MadhuraChoudhary/GuardianSense-AI_Health_Monitor_system/COMPONENT INTERACTION DIAGRAM.png

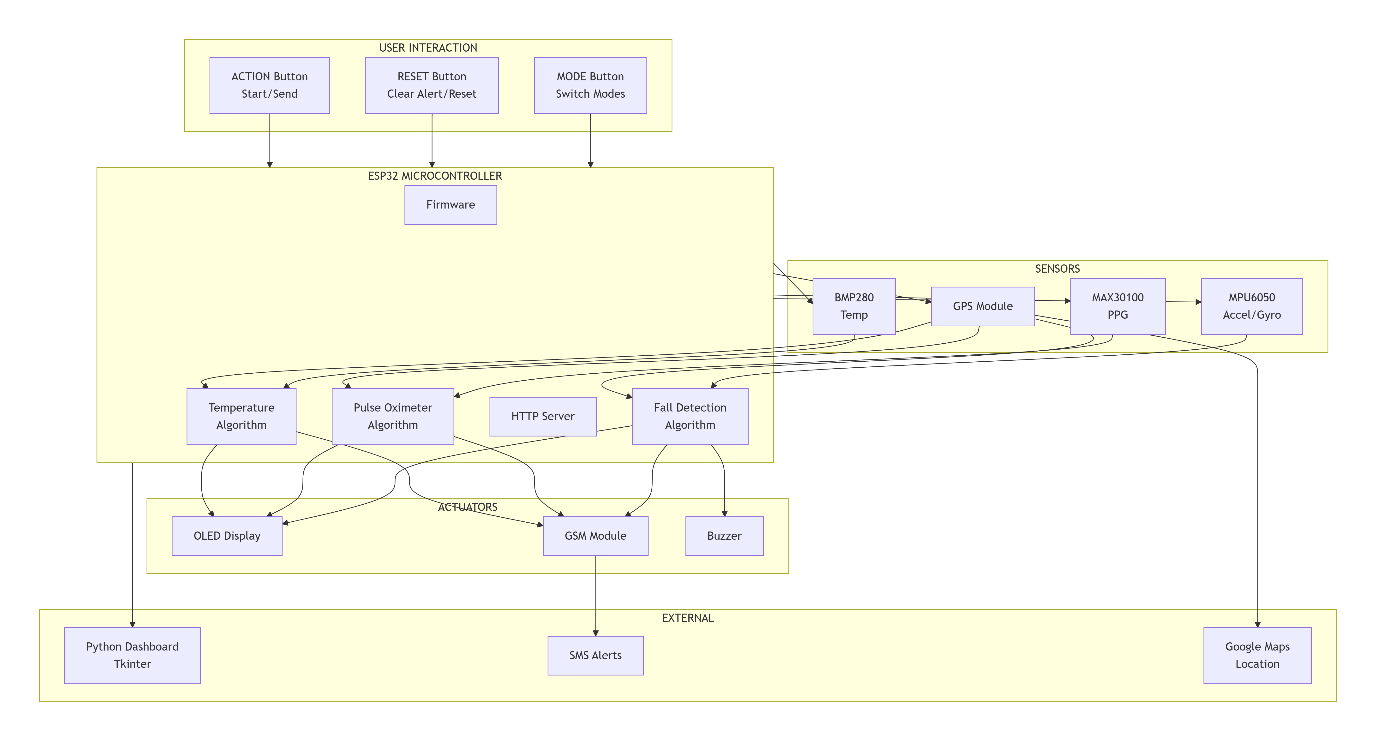
COMPONENT INTERACTION DIAGRAM.png
